frixo3190/acw02_esphome/notUsed/pcb lolin c3 mini - xiao C3-C6/front.PNG

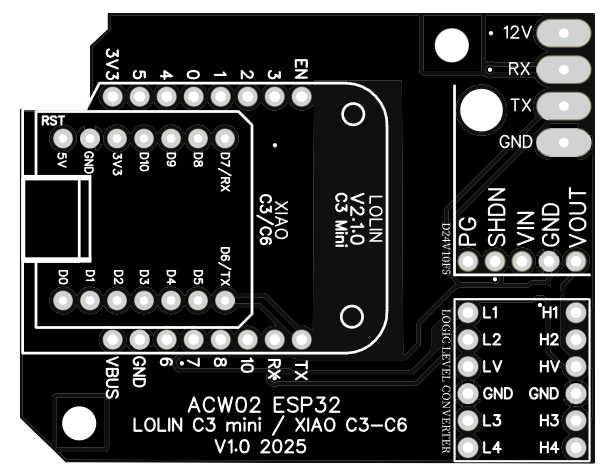
notUsed/pcb lolin c3 mini - xiao C3-C6/front.PNG
