frixo3190/acw02_esphome/notUsed/proto pcb for replace level shiffter/annexe/img.PNG

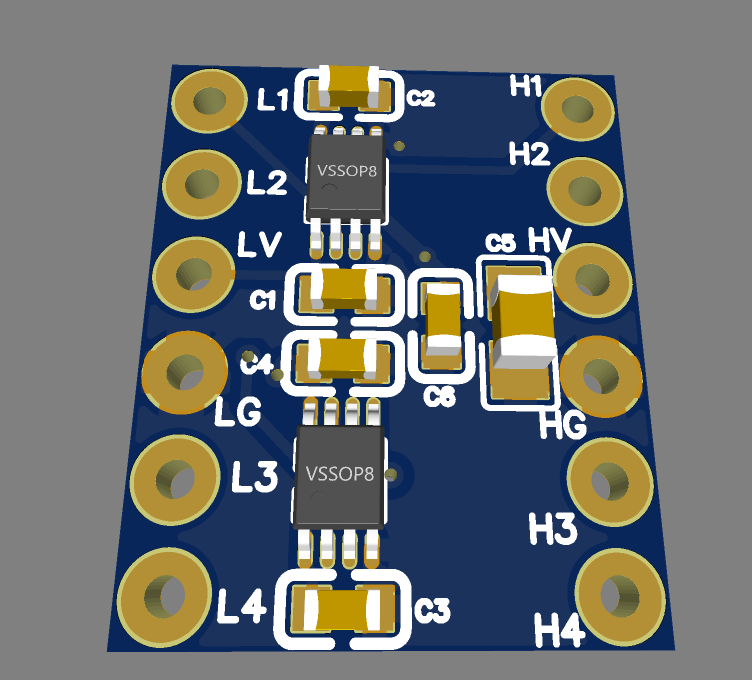
notUsed/proto pcb for replace level shiffter/annexe/img.PNG
