frixo3190/acw02_esphome/notUsed/unmount/buzzer.PNG

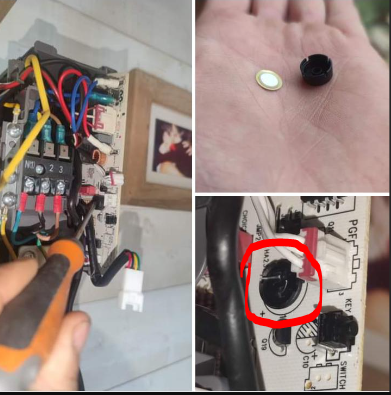
notUsed/unmount/buzzer.PNG
