frixo3190/acw02_esphome/PCB/pcb-usb-adapter/usb-adapter.png

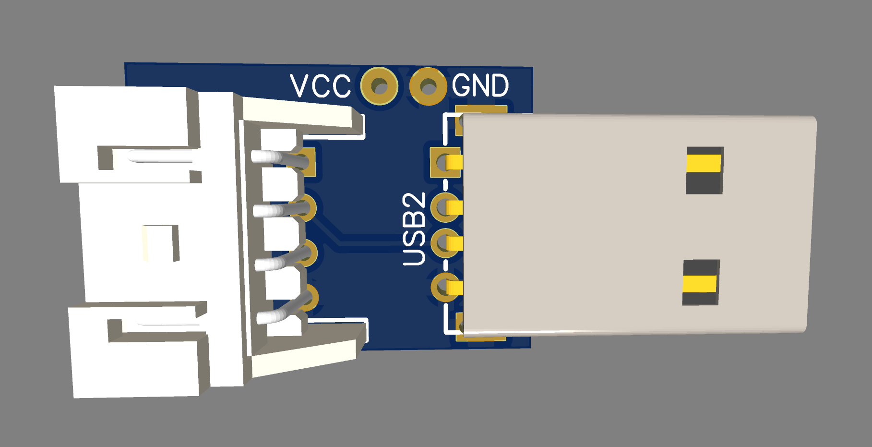
PCB/pcb-usb-adapter/usb-adapter.png
