frixo3190/acw02_esphome/PCB/images/components/ESP32-WROOM-32 D1 Mini NodeMCU.PNG

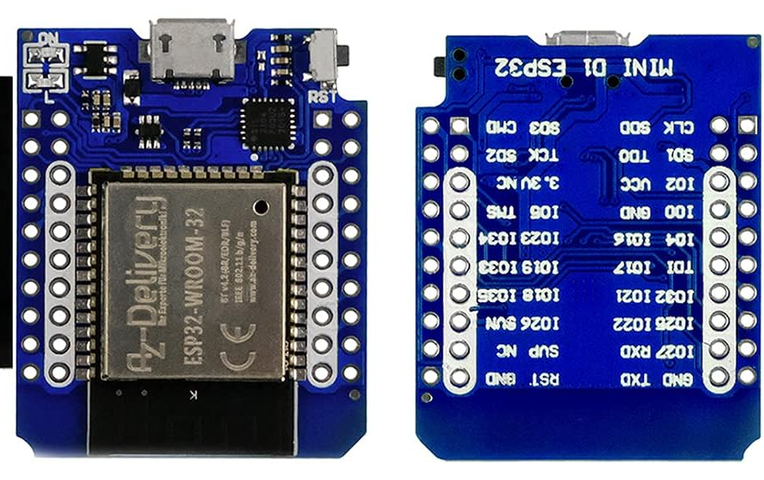
PCB/images/components/ESP32-WROOM-32 D1 Mini NodeMCU.PNG
