frixo3190/acw02_esphome/PCB/images/components/SN74LVC2T45DCUR.PNG

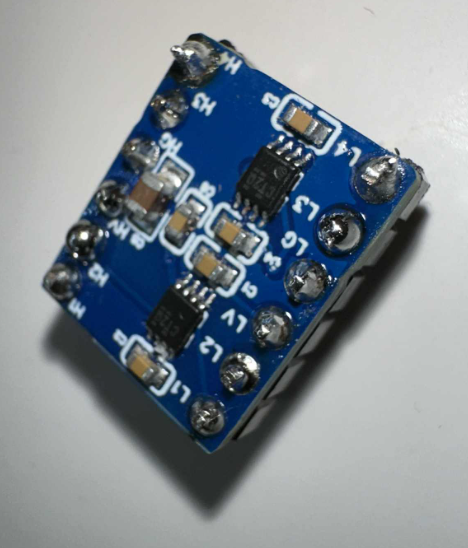
PCB/images/components/SN74LVC2T45DCUR.PNG
