frixo3190/acw02_esphome/3Dfiles/D1-MIMI/Version 2/acw02 case top air flow.stl

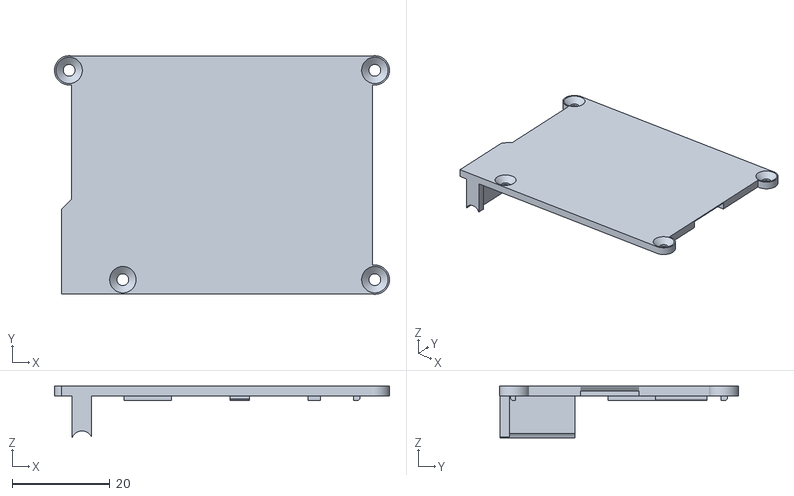
[picture p124: CAD file, 2025-07-23]
3Dfiles/D1-MIMI/Version 2/acw02 case top air flow.stl
68.6 x 48.9 x 10.6
