frixo3190/acw02_esphome/3Dfiles/LOLIN-C3-XIAO-C3-C6/button lolin c3.stl

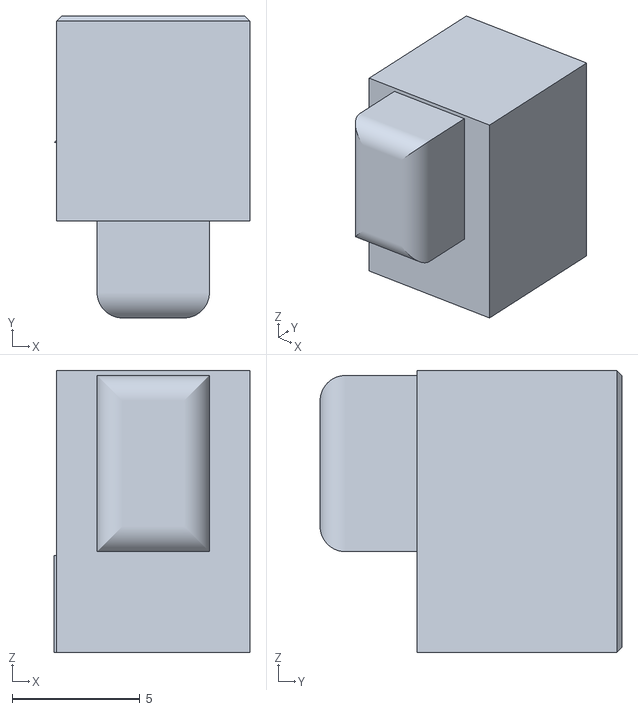
[picture p125: CAD file, 2026-06-21]
3Dfiles/LOLIN-C3-XIAO-C3-C6/button lolin c3.stl
7.67 x 11.8 x 11.0
