frixo3190/acw02_esphome/3Dfiles/D1-MIMI/Version 2/acw02 case top cable with thermo plastic card.stl

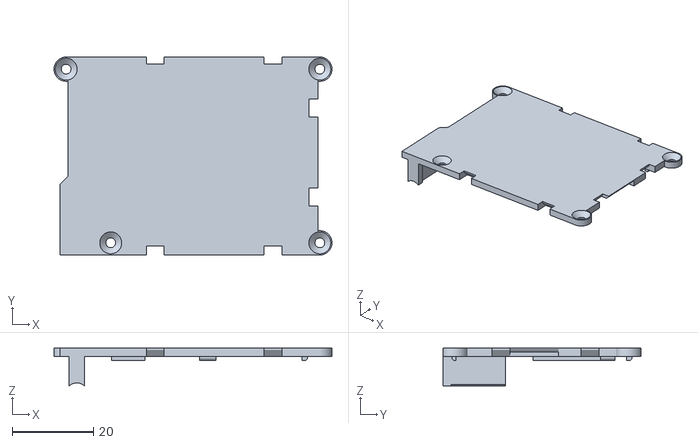
[picture p126: CAD file, 2025-07-23]
3Dfiles/D1-MIMI/Version 2/acw02 case top cable with thermo plastic card.stl
68.6 x 48.9 x 9.30
