frixo3190/acw02_esphome/3Dfiles/LOLIN-C3-XIAO-C3-C6/support antenna rigid part A.stl

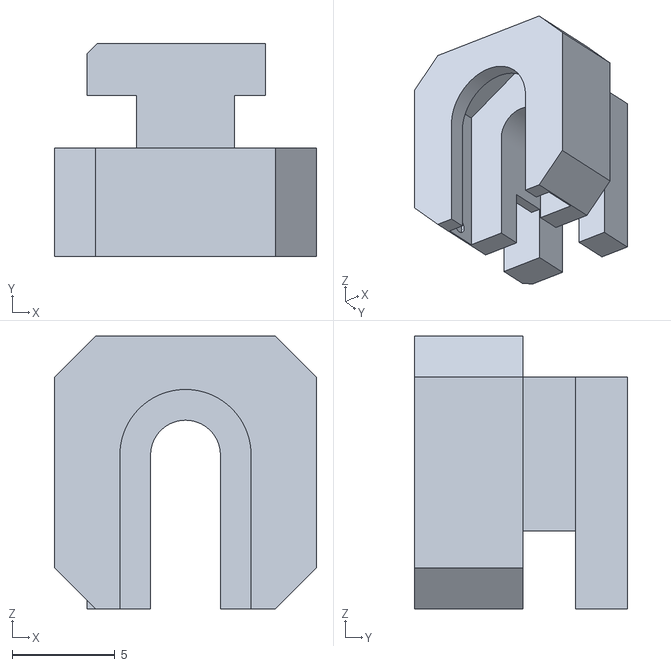
[picture p127: CAD file, 2026-06-21]
3Dfiles/LOLIN-C3-XIAO-C3-C6/support antenna rigid part A.stl
12.8 x 10.4 x 13.3
