frixo3190/acw02_esphome/PCB/images/components/esp32 solder pins.png

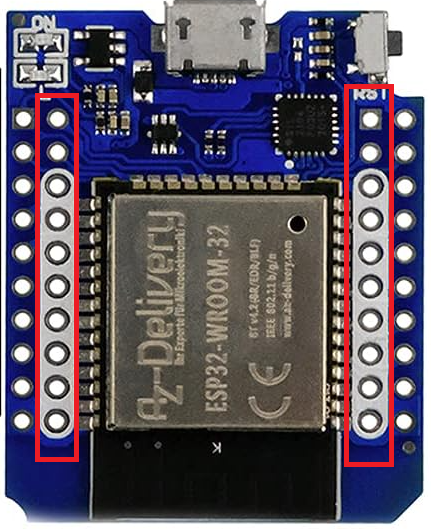
PCB/images/components/esp32 solder pins.png
